hanafi9/s3-salle-de-bain/cad/boitier_v5/v5_base.step

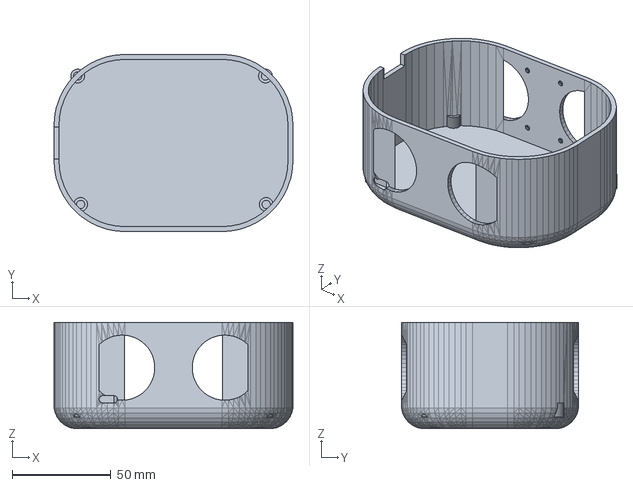
[picture p28: CAD file, 2026-06-17, an earlier design]
cad/boitier_v5/v5_base.step
121.1 x 89.7 x 53.9 mm
