hanafi9/s3-salle-de-bain/kicad/kicad_std_symbols.py

STD_SYMBOLS = r"""
    (symbol "Device:R"
    		(pin_numbers
    			(hide yes)
    		)
    		(pin_names
    			(offset 0)
    		)
    		(exclude_from_sim no)
    		(in_bom yes)
    		(on_board yes)
    		(in_pos_files yes)
    		(duplicate_pin_numbers_are_jumpers no)
    		(property "Reference" "R"
    			(at 2.032 0 90)
    			(show_name no)
    			(do_not_autoplace no)
    			(effects
    				(font
    					(size 1.27 1.27)
    				)
    			)
    		)
    		(property "Value" "R"
    			(at 0 0 90)
    			(show_name no)
    			(do_not_autoplace no)
    			(effects
    				(font
    					(size 1.27 1.27)
    				)
    			)
    		)
    		(property "Footprint" ""
    			(at -1.778 0 90)
    			(show_name no)
    			(do_not_autoplace no)
    			(hide yes)
    			(effects
    				(font
    					(size 1.27 1.27)
    				)
    			)
    		)
    		(property "Datasheet" ""
    			(at 0 0 0)
    			(show_name no)
    			(do_not_autoplace no)
    			(hide yes)
    			(effects
    				(font
    					(size 1.27 1.27)
    				)
    			)
    		)
    		(property "Description" "Resistor"
    			(at 0 0 0)
    			(show_name no)
    			(do_not_autoplace no)
    			(hide yes)
    			(effects
    				(font
    					(size 1.27 1.27)
    				)
    			)
    		)
    		(property "ki_keywords" "R res resistor"
    			(at 0 0 0)
    			(show_name no)
    			(do_not_autoplace no)
    			(hide yes)
    			(effects
    				(font
    					(size 1.27 1.27)
    				)
    			)
    		)
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
    				)
    			)
    		)
    		(symbol "PWR_FLAG_0_0"
    			(pin power_out line
    				(at 0 0 90)
    				(length 0)
    				(name ""
    					(effects
    						(font
    							(size 1.27 1.27)
    						)
    					)
    				)
    				(number "1"
    					(effects
    						(font
    							(size 1.27 1.27)
    						)
    					)
    				)
    			)
    		)
    		(symbol "PWR_FLAG_0_1"
    			(polyline
    				(pts
    					(xy 0 0) (xy 0 1.27) (xy -1.016 1.905) (xy 0 2.54) (xy 1.016 1.905) (xy 0 1.27)
    				)
    				(stroke
    					(width 0)
    					(type default)
    				)
    				(fill
    					(type none)
    				)
    			)
    		)
    		(embedded_fonts no)
    	)
"""
